knr-at-iaac/cultivation-furniture-0.0.1/glasscuttingWTRI.JPEG

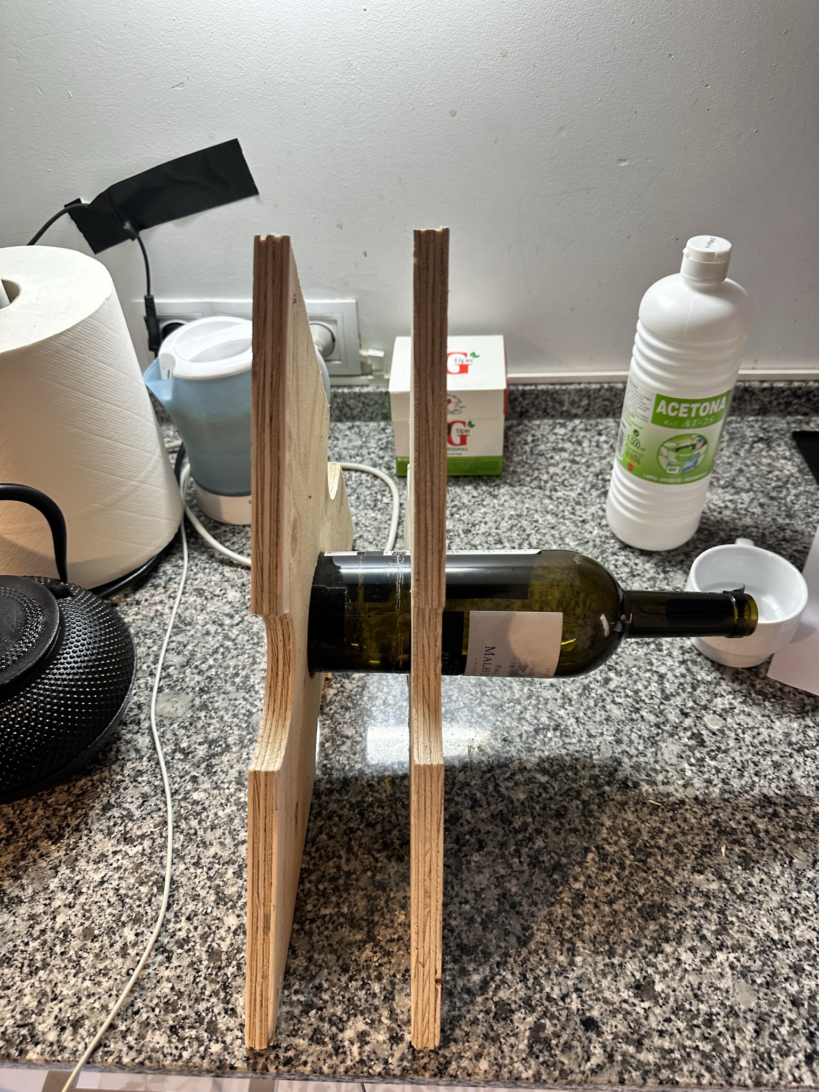
glasscuttingWTRI.JPEG
