knr-at-iaac/cultivation-furniture-0.0.1/modular.JPEG

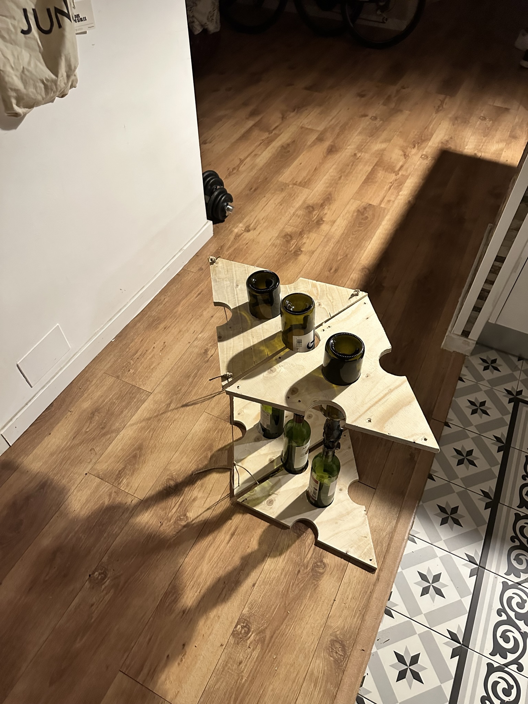
modular.JPEG
