knr-at-iaac/cultivation-furniture-0.0.1/OIL.JPEG

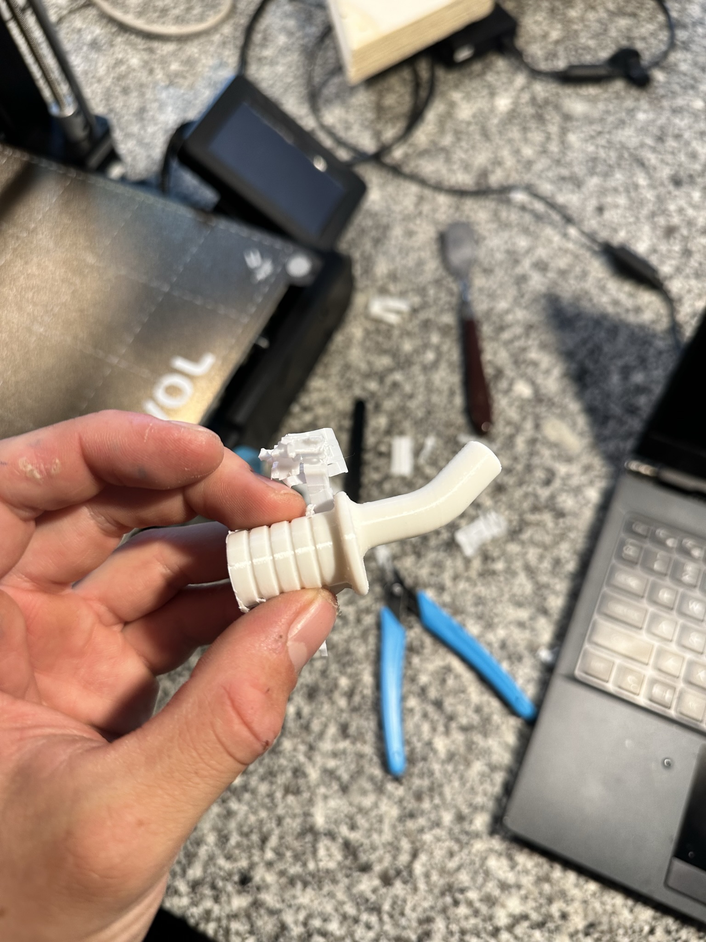
OIL.JPEG
