knr-at-iaac/cultivation-furniture-0.0.1/shittyCut.JPEG

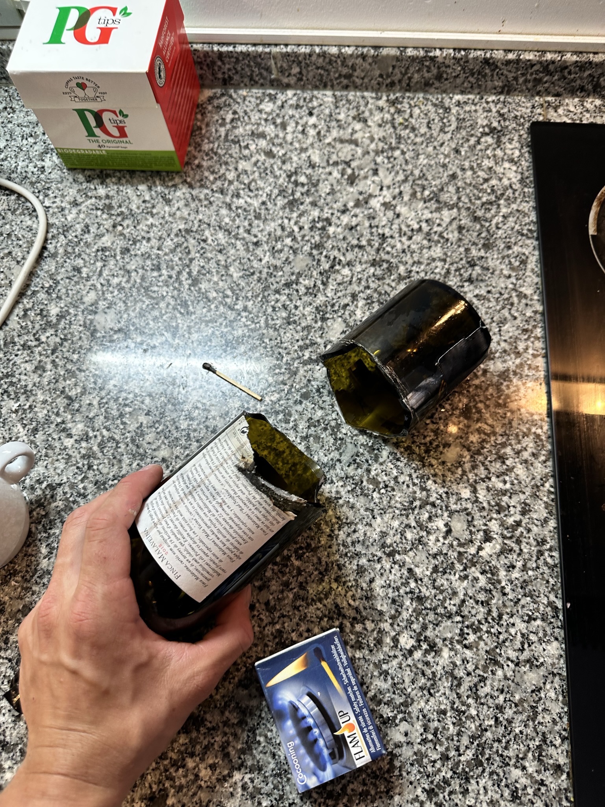
shittyCut.JPEG
