knr-at-iaac/cultivation-furniture-0.0.1/sizeBottle.JPEG

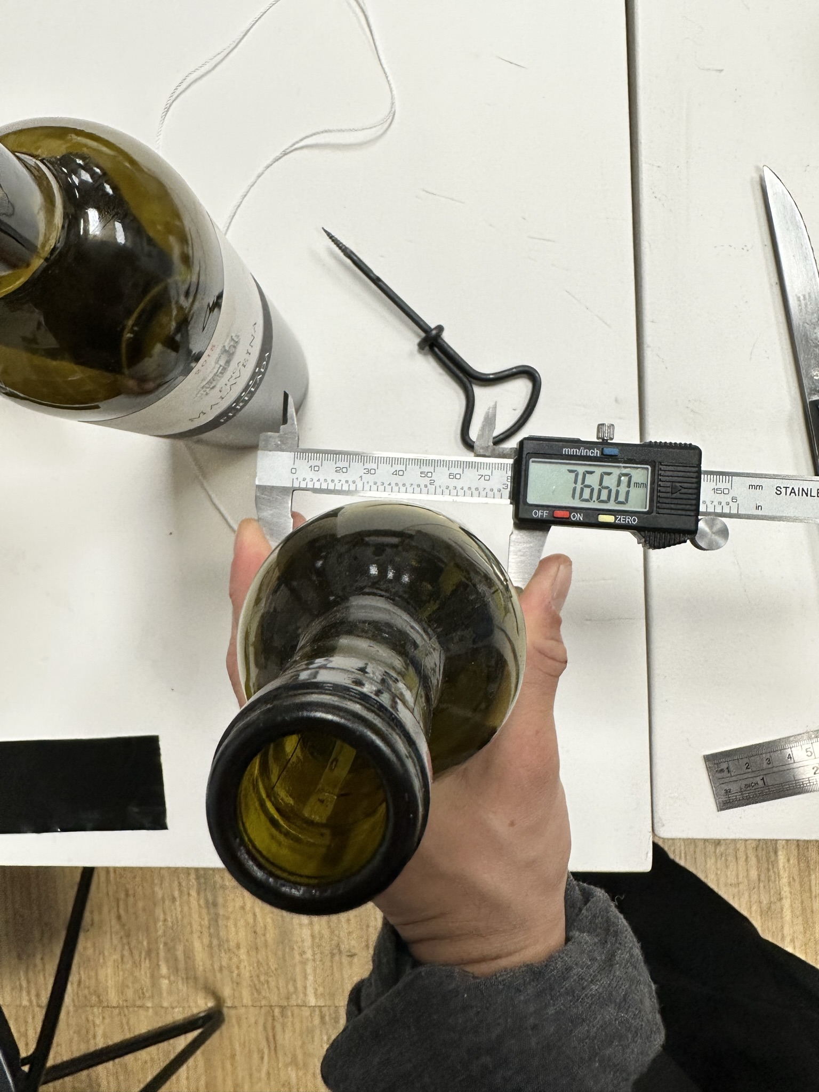
sizeBottle.JPEG
