knr-at-iaac/cultivation-furniture-0.0.1/STRINGTOCUT.JPEG

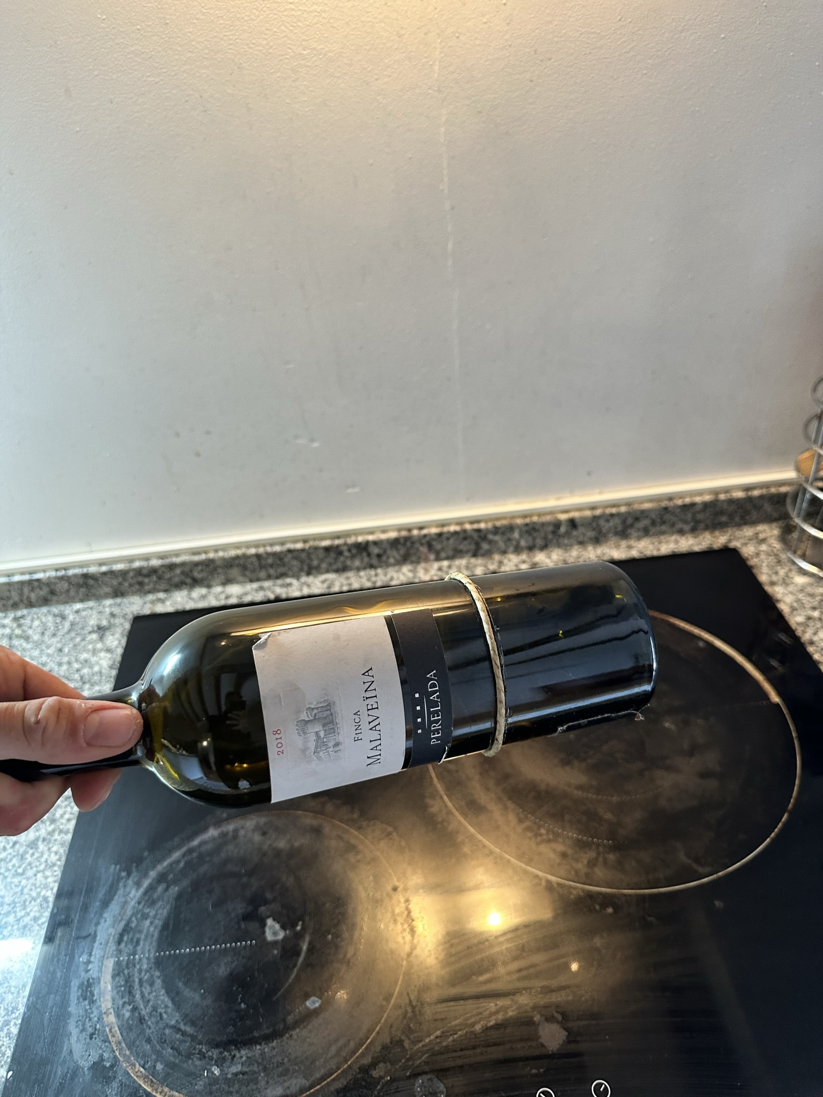
STRINGTOCUT.JPEG
