knr-at-iaac/cultivation-furniture-0.0.1/usingTapeToCut.JPEG

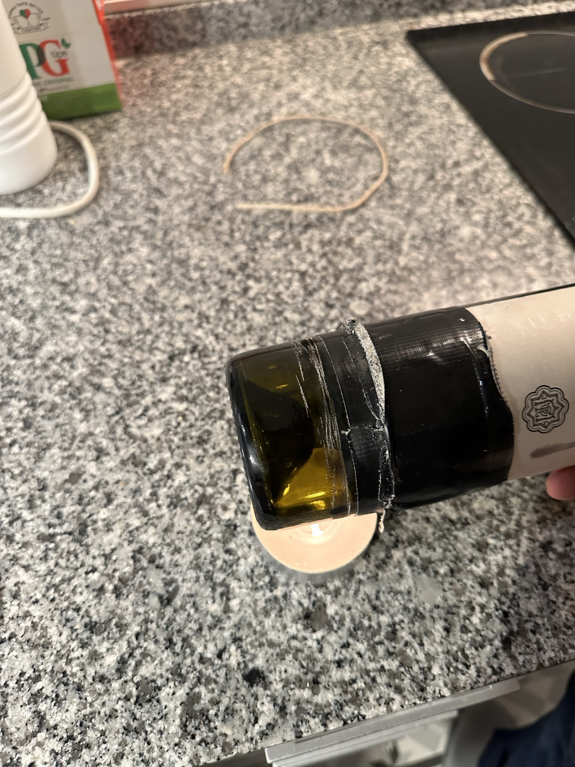
usingTapeToCut.JPEG
