knr-at-iaac/cultivation-furniture-0.0.1/building.JPEG

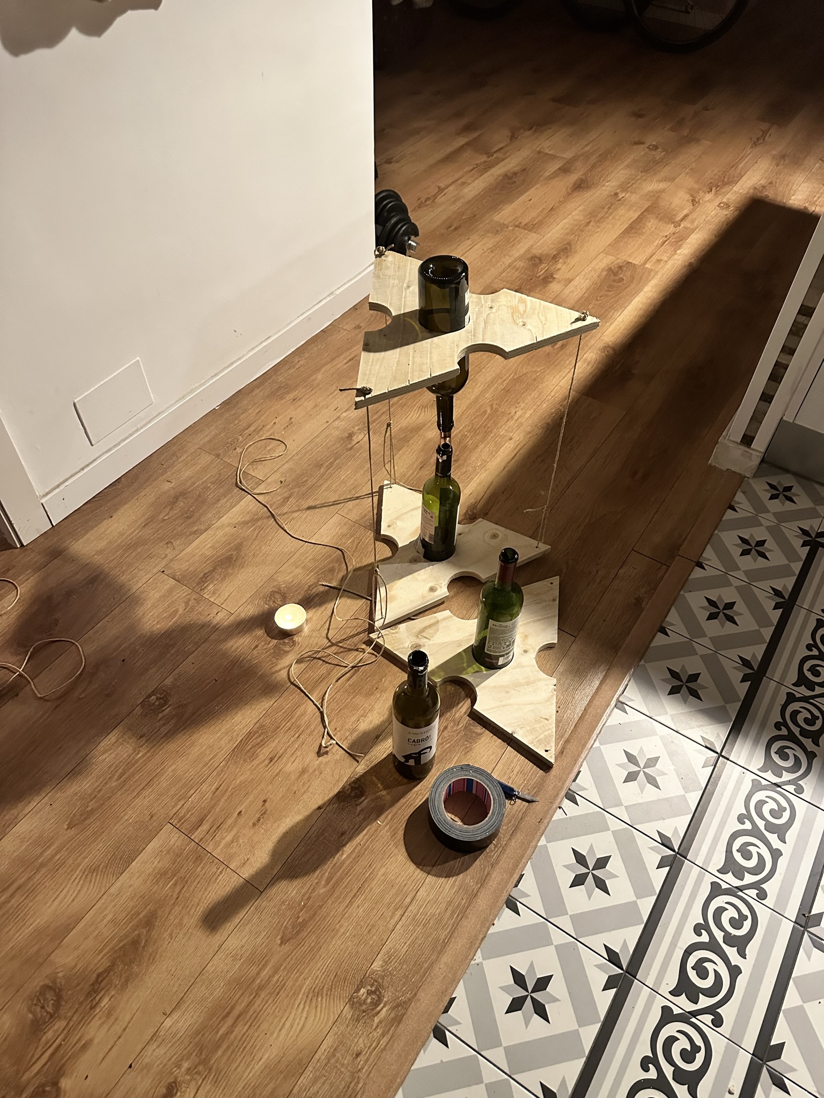
building.JPEG
