knr-at-iaac/cultivation-furniture-0.0.1/CutSetup.JPEG

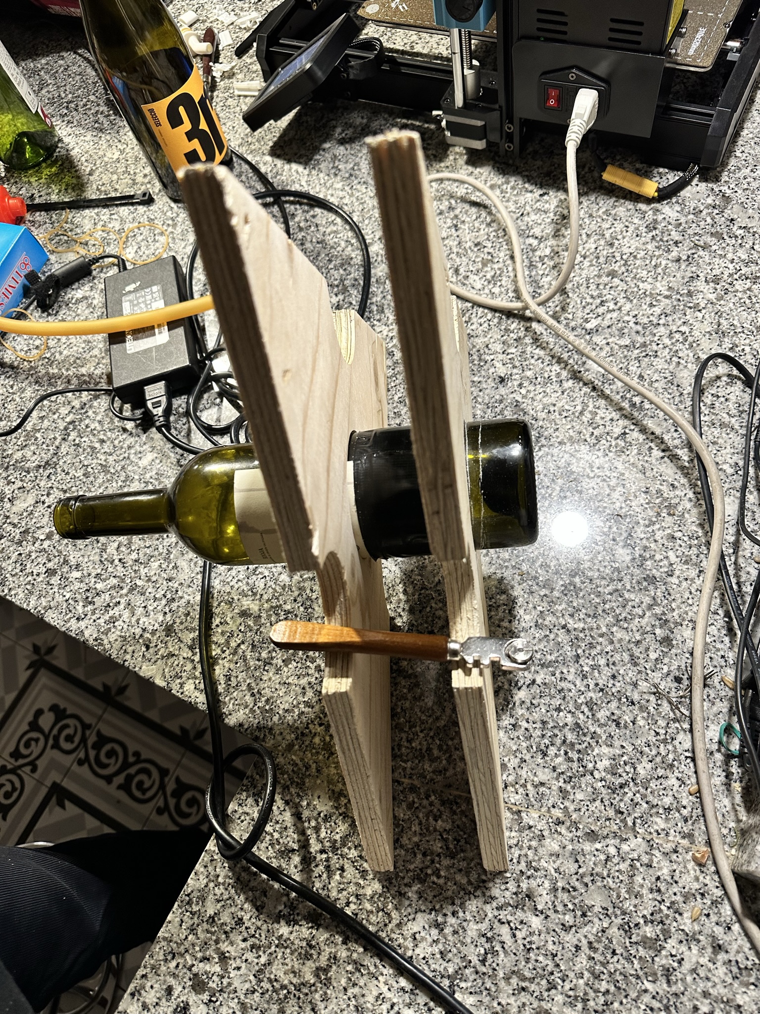
CutSetup.JPEG
