knr-at-iaac/cultivation-furniture-0.0.1/glassSETUP.JPEG

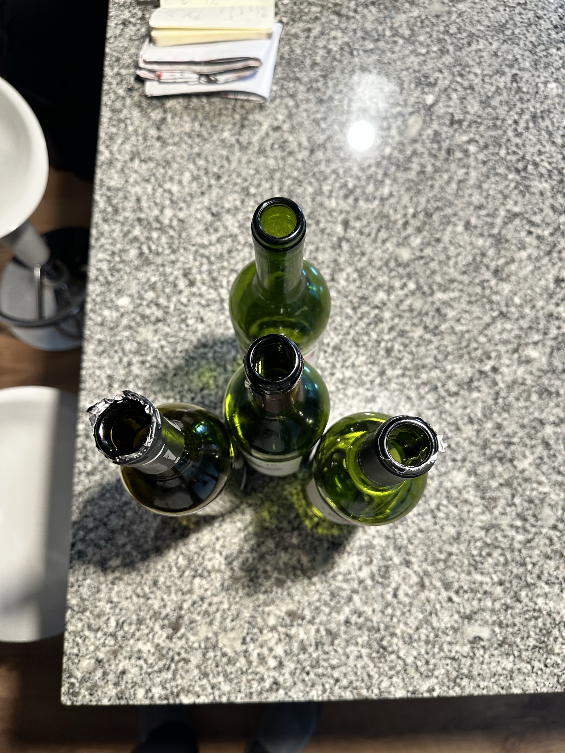
glassSETUP.JPEG
